silveirago/Faduino/_Faduino_2023_10_18/FUNCTIONS.ino

////////////////////////////////////////////
// checks if it's greater than maximum value or less than then the minimum value
int clipValue(int in, int minVal, int maxVal) {

  int out;

  minVal++;

  if (in > maxVal) {
    out = maxVal;
  } else if (in < minVal) {
    out = minVal - 1;
  } else {
    out = in;
  }

  return out;
}

int linToLog(int in_, int size_) {
  float a = in_ / size_;
  float b = sqrtf(a);
  float c = b * size_;

  return int(c);
}
